afonsus1997/Bongo-Cat-Fidget-Toy/Media/Photos/PXL_20250726_182516591.MACRO_FOCUS.MP~2.jpg

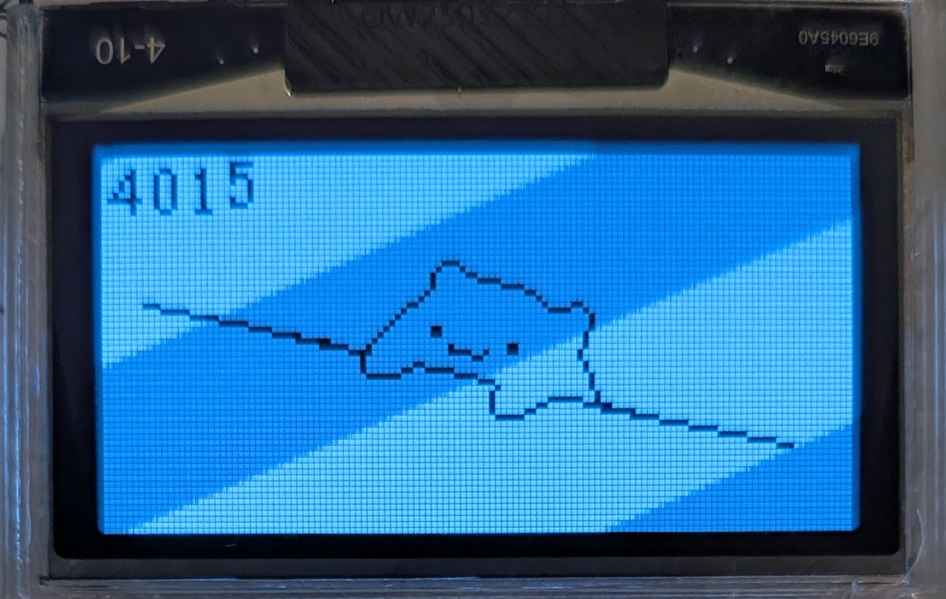
Media/Photos/PXL_20250726_182516591.MACRO_FOCUS.MP~2.jpg
