afonsus1997/Bongo-Cat-Fidget-Toy/Hardware/3D/LCD Support - LCD Support-1.STL

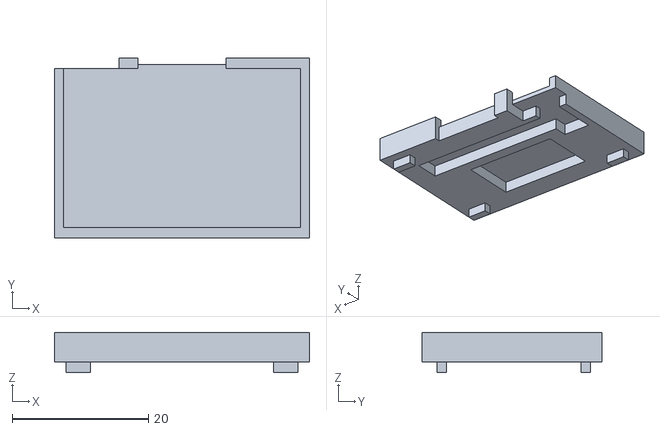
[picture p20: CAD file, 2026-04-17]
Hardware/3D/LCD Support - LCD Support-1.STL
37.5 x 26.5 x 5.95
