afonsus1997/Bongo-Cat-Fidget-Toy/Hardware/3D/LCD Support - Bongo-Cat-Fidget-Toy.step-1 R_0603_1608Metric.step-2.STL

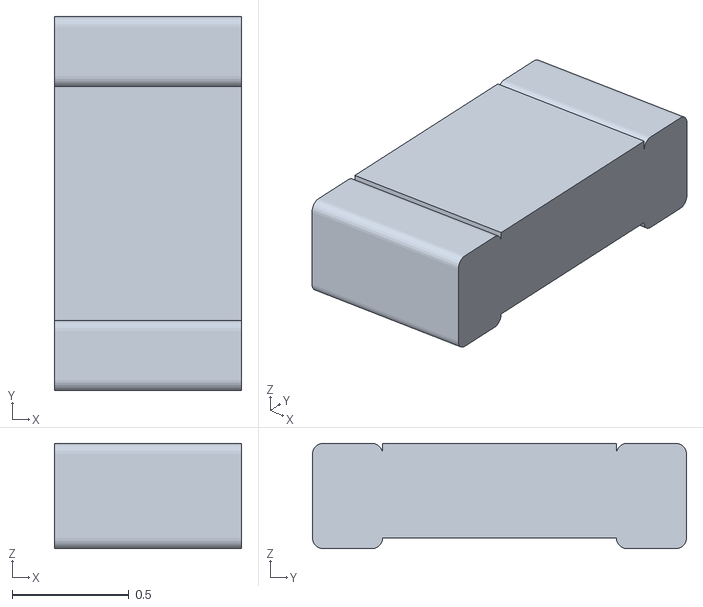
[picture p21: CAD file, 2026-04-17]
Hardware/3D/LCD Support - Bongo-Cat-Fidget-Toy.step-1 R_0603_1608Metric.step-2.STL
0.8 x 1.60 x 0.45
