afonsus1997/Bongo-Cat-Fidget-Toy/Hardware/3D/LCD Support - Bongo-Cat-Fidget-Toy.step-1 SW-SMD_SK-3245S-L1-A-1.step-1 SOLID.step-1.STL

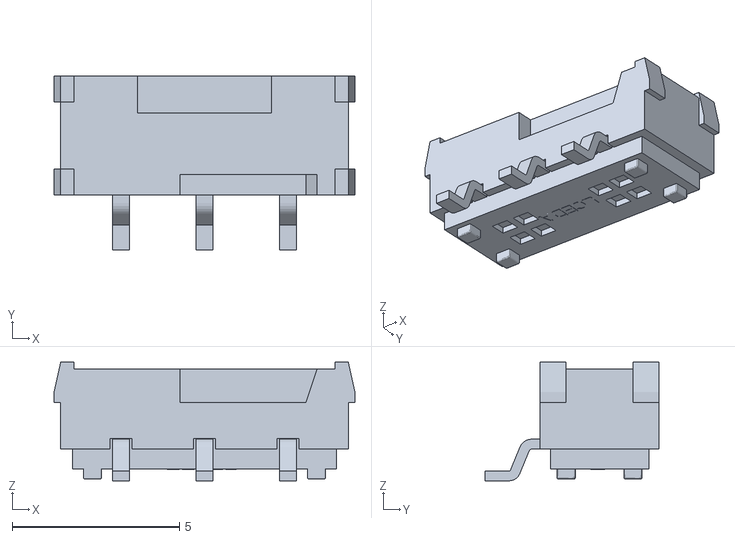
[picture p22: CAD file, 2026-04-17]
Hardware/3D/LCD Support - Bongo-Cat-Fidget-Toy.step-1 SW-SMD_SK-3245S-L1-A-1.step-1 SOLID.step-1.STL
9.00 x 5.20 x 3.55
