afonsus1997/Bongo-Cat-Fidget-Toy/Hardware/3D/LCD Support - Bongo-Cat-Fidget-Toy.step-1 L_Wurth_WE-L__010.step-1 L_Wurth_WE-LQSH-2010-2.step-1.STL

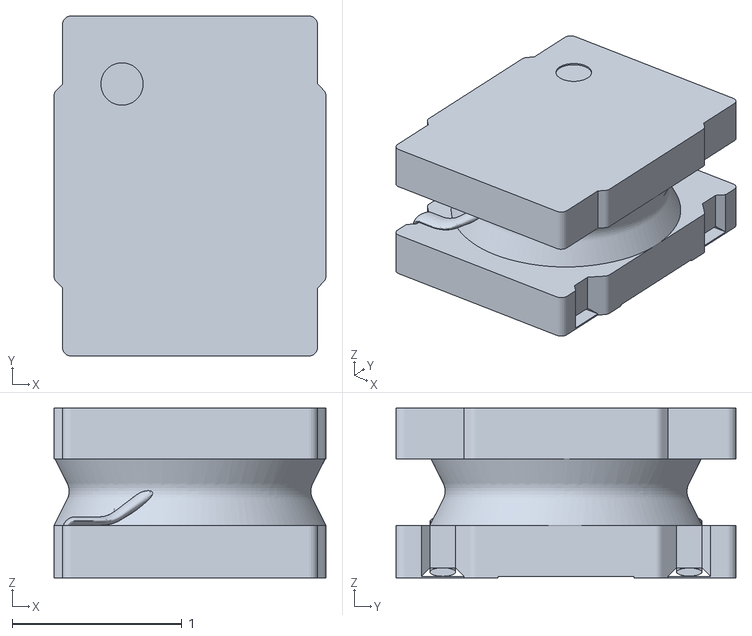
[picture p23: CAD file, 2026-04-17]
Hardware/3D/LCD Support - Bongo-Cat-Fidget-Toy.step-1 L_Wurth_WE-L__010.step-1 L_Wurth_WE-LQSH-2010-2.step-1.STL
1.60 x 2.00 x 1.00
