afonsus1997/Bongo-Cat-Fidget-Toy/Hardware/3D/LCD Support - Bongo-Cat-Fidget-Toy.step-1 Bongo-Cat-Fidget-Toy_PCB.step-1.STL

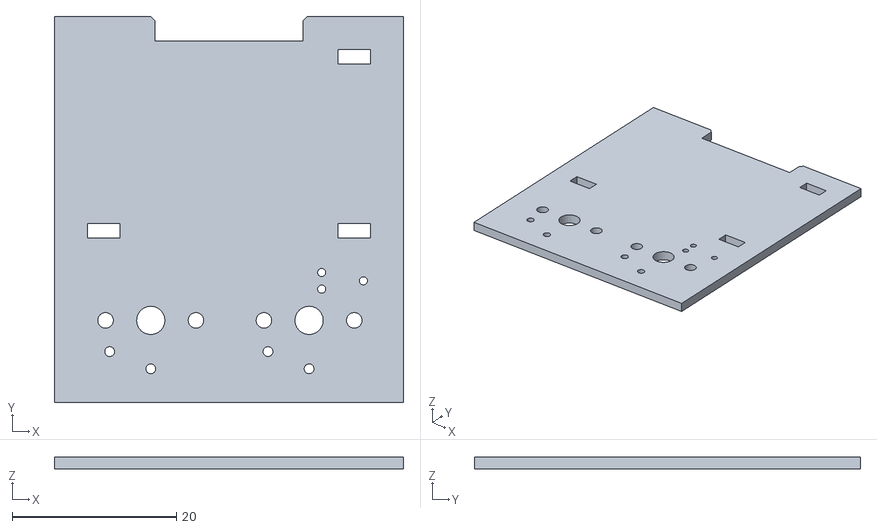
[picture p24: CAD file, 2026-04-17]
Hardware/3D/LCD Support - Bongo-Cat-Fidget-Toy.step-1 Bongo-Cat-Fidget-Toy_PCB.step-1.STL
42.5 x 47.0 x 1.51
