afonsus1997/Bongo-Cat-Fidget-Toy/Software/Bongo-Cat-Fidget-Toy-Py32/App/bitmaps.h

#ifndef __BITMAPS__H__
#define __BITMAPS__H__

// 'both_down', 128x64px
extern const unsigned char img_both_down [];
// 'both_up', 128x64px
extern const unsigned char img_both_up [];
// 'idle1', 128x64px
extern const unsigned char img_idle1 [];
// 'idle2', 128x64px
extern const unsigned char img_idle2 [];
// 'idle3', 128x64px
extern const unsigned char img_idle3 [];
// 'idle4', 128x64px
extern const unsigned char img_idle4 [];
// 'idle5', 128x64px
extern const unsigned char img_idle5 [];
// 'left_down', 128x64px
extern const unsigned char img_left_down [];
// 'right_down', 128x64px
extern const unsigned char img_right_down [];

// Array of all bitmaps for convenience. (Total bytes used to store images in = 9360)
// Array of all bitmaps for convenience. (Total bytes used to store images in = 9360)
extern const int ani_idle_LEN;
extern const unsigned char* ani_idle[5];

// ALT

// 'both_down_alt', 128x64px
extern const unsigned char img_both_down_alt [];
// 'left_down_alt', 128x64px
extern const unsigned char img_left_down_alt [];
// 'right_down_alt', 128x64px
extern const unsigned char img_right_down_alt [];
// 'tap_left', 128x64px
extern const unsigned char img_tap_left [];
// 'tap_right', 128x64px
extern const unsigned char img_tap_right[];
// 'idle_sleep', 128x64px
extern const unsigned char img_idle_sleep [];

#endif  //!__BITMAPS__H__
