afonsus1997/Bongo-Cat-Fidget-Toy/Software/Bongo-Cat-Fidget-Toy-Py32/App/bitmaps_angry.h

#ifndef __BITMAPS_ANGRY__H__
#define __BITMAPS_ANGRY__H__

// 'both_down_alt_angry', 128x64px
extern const unsigned char img_both_down_alt_angry [];
// 'both_down_angry', 128x64px
extern const unsigned char img_both_down_angry [];
// 'both_up_angry', 128x64px
extern const unsigned char img_both_up_angry [];
// 'left_down', 128x64px
extern const unsigned char img_left_down_angry [];
// 'left_down_alt_angry', 128x64px
extern const unsigned char img_left_down_alt_angry [];
// 'right_down_alt_angry', 128x64px
extern const unsigned char img_right_down_alt_angry [];
// 'right_down_angry', 128x64px
extern const unsigned char img_right_down_angry [];

#endif  //!__BITMAPS_ANGRY__H__
